stianeklund/ARCI-Enclosure/docs/visual-reference/original-front-internal-supports-annotated.png

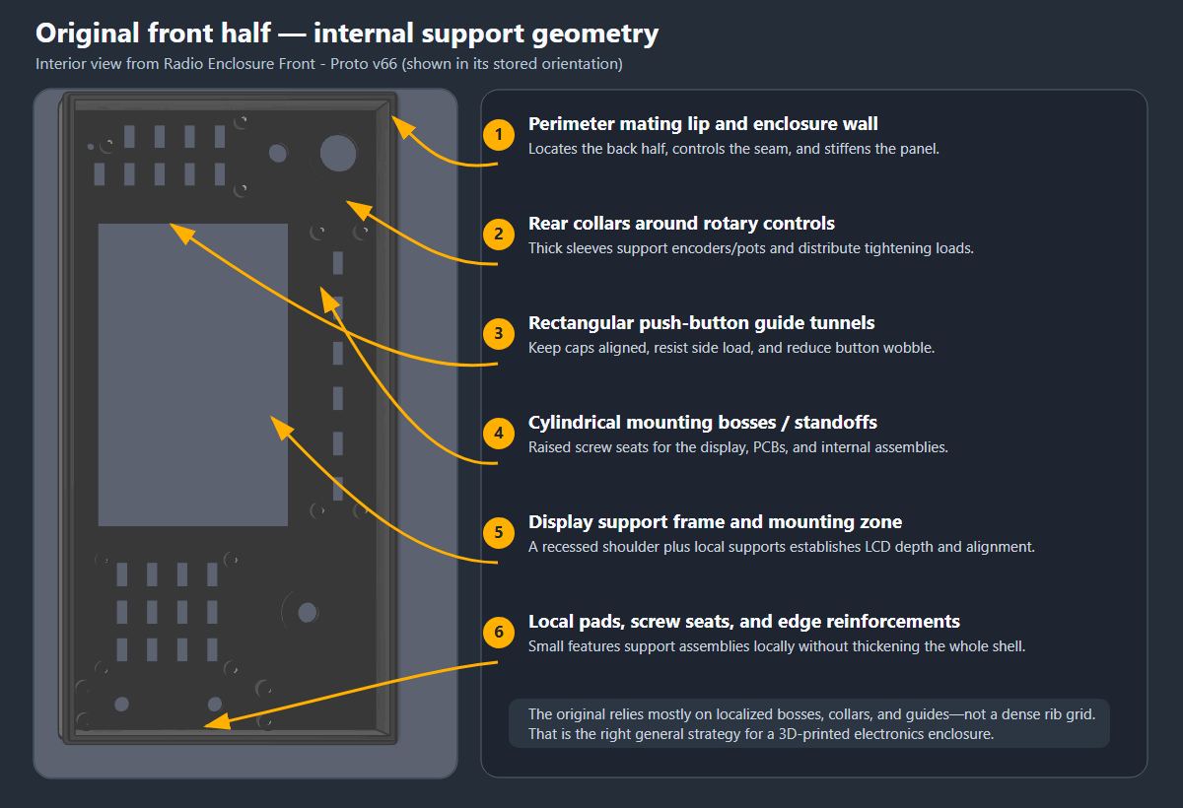
docs/visual-reference/original-front-internal-supports-annotated.png
