stianeklund/ARCI-Enclosure/images/renders/rev3-rear.png

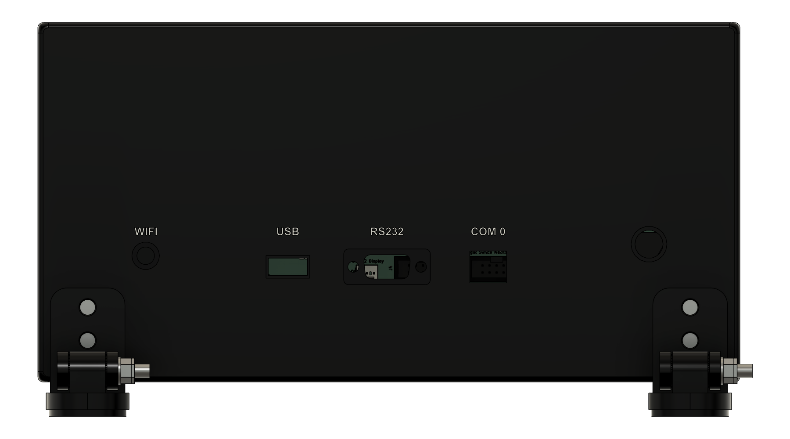
images/renders/rev3-rear.png
