stianeklund/ARCI-Enclosure/images/renders/rev3-stand-hinge.png

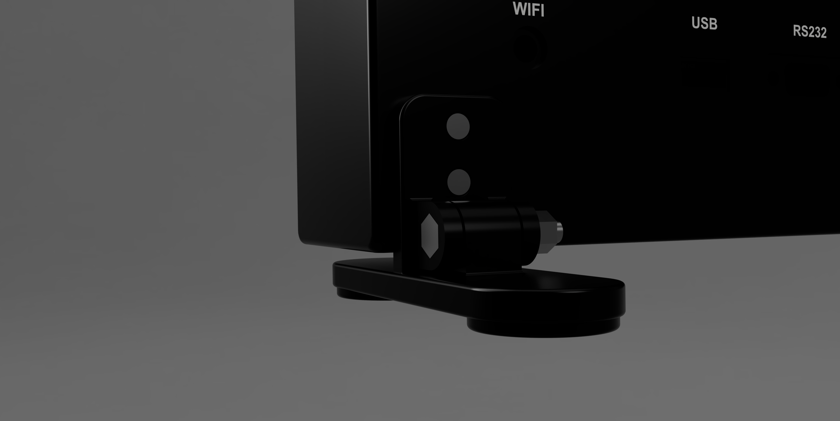
images/renders/rev3-stand-hinge.png
